RTZR4308/PrintModels/Other/Tube_fixator.stl

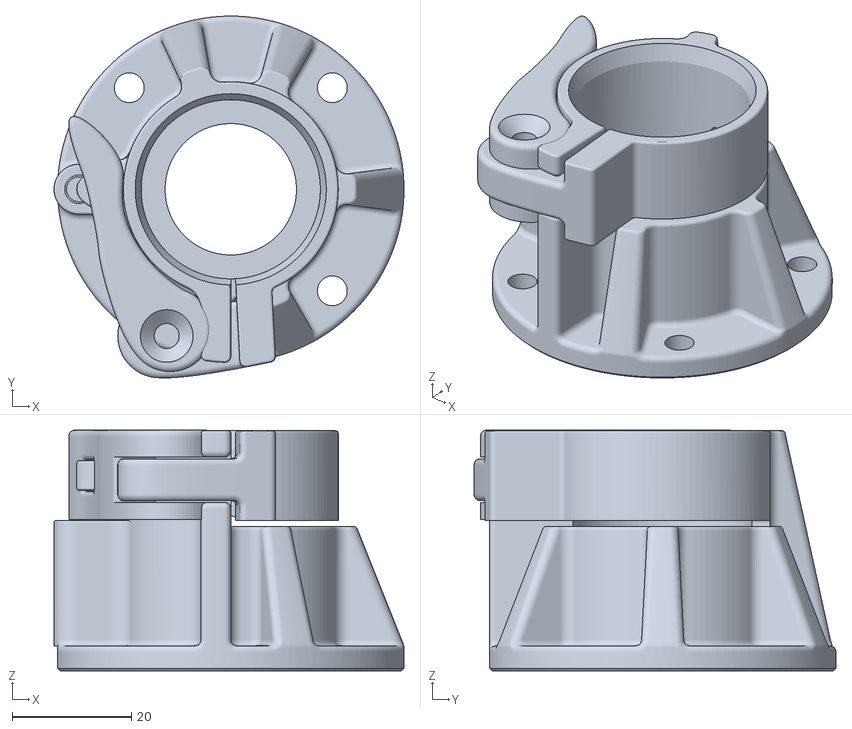
[picture p15: CAD file, 2025-07-25]
Other/Tube_fixator.stl
58.6 x 60.6 x 40.3
