RTZR4308/PrintModels/Starlink/Reductor Starlink.step

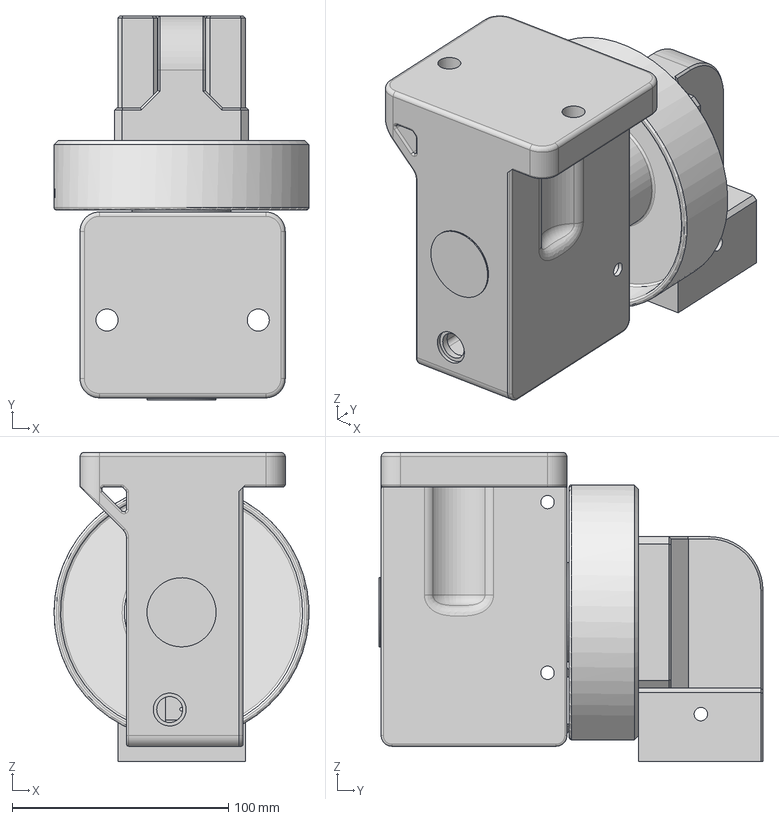
[picture p16: CAD file, 2025-03-28]
Starlink/Reductor Starlink.step
117.9 x 177.7 x 143.1 mm
OutputFile
BS 4320 - M6 G Steel 100 HV Plain
DIN 933 - M6 x 80 Steel 4.6 Plain x 2
DIN 912 - M5 x 0.8 x 20 Steel 4.6 Plain x 4
