RTZR4308/PrintModels/Autel/autel_4tmax_leg_rf.stl

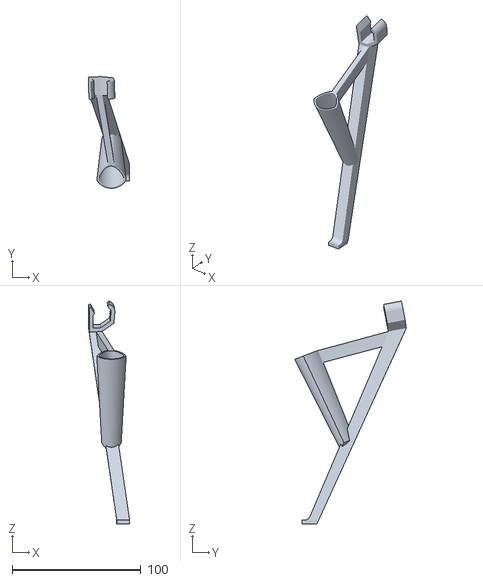
[picture p17: CAD file, 2024-12-12]
Autel/autel_4tmax_leg_rf.stl
32.1 x 86.9 x 173.5
