RTZR4308/PrintModels/Autel/Dual Bat/autel_top_holder_front_V2.STL

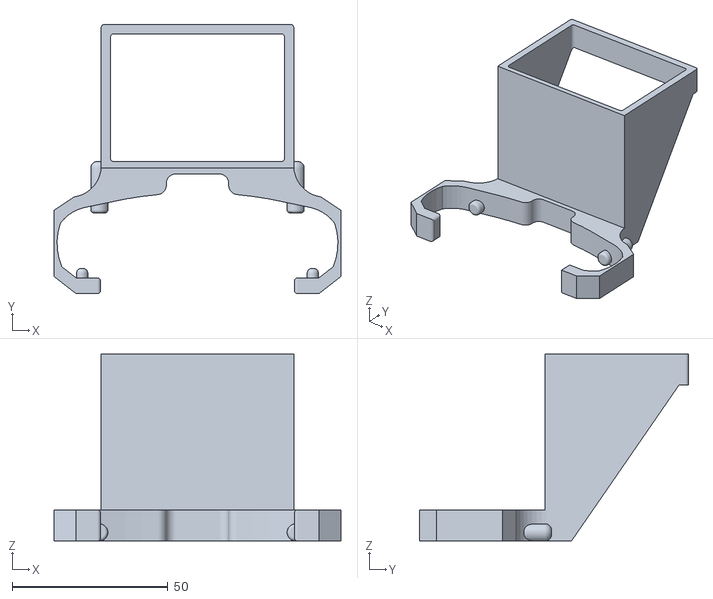
[picture p18: CAD file, 2025-02-19]
Autel/Dual Bat/autel_top_holder_front_V2.STL
92.1 x 86.4 x 60.0
