RTZR4308/PrintModels/Controllers/rm510_4Ntype_Mount_air.STL

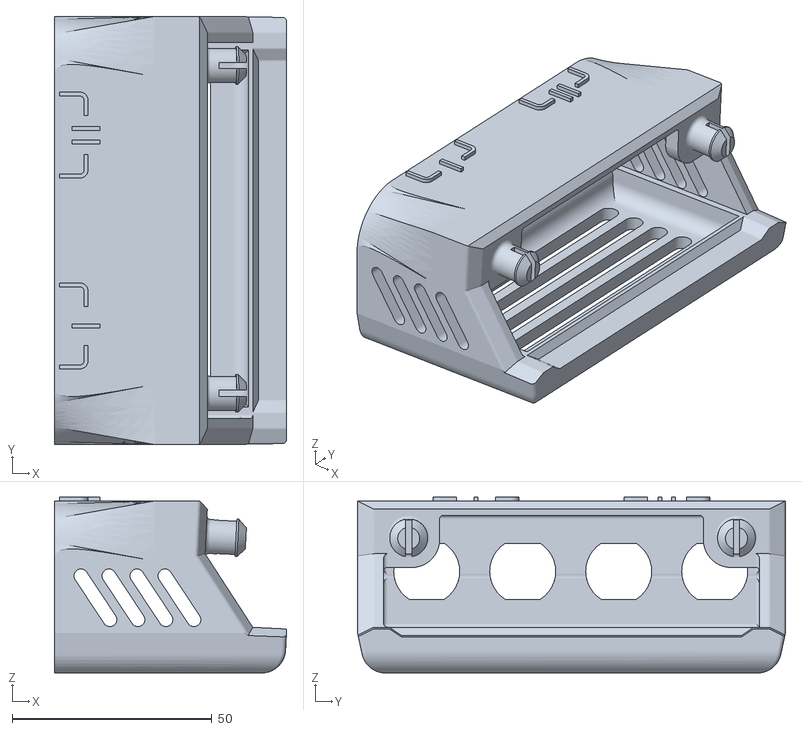
[picture p19: CAD file, 2024-12-12]
Controllers/rm510_4Ntype_Mount_air.STL
58.1 x 107.0 x 44.0
