RTZR4308/PrintModels/DJI/M3/Dual Bat/dji_m3_dual_bat_fpv_99scale_8parts_x1c.3mf

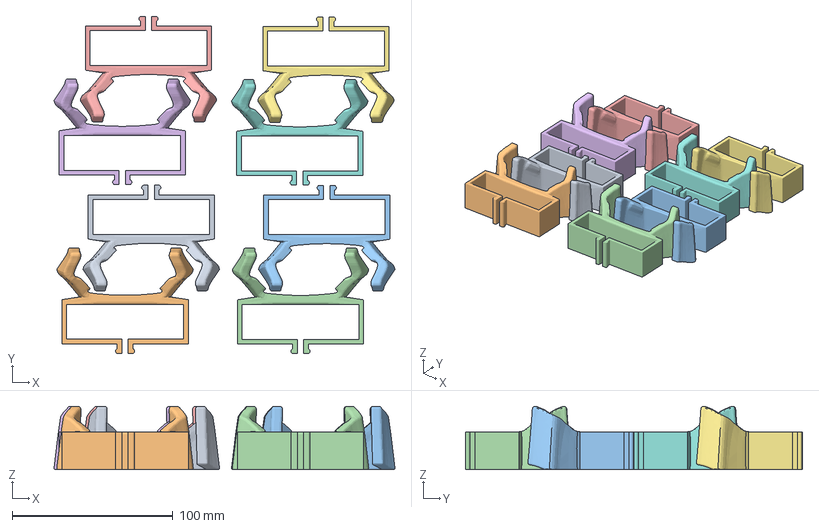
[picture p20: CAD file, 2025-01-25]
DJI/M3/Dual Bat/dji_m3_dual_bat_fpv_99scale_8parts_x1c.3mf
212.1 x 209.9 x 39.4 mm
dji_m3_dual_bat_fpv.stl x 8
