RTZR4308/PrintModels/DJI/M3/Legs/dji_m3_leg_bl.stl

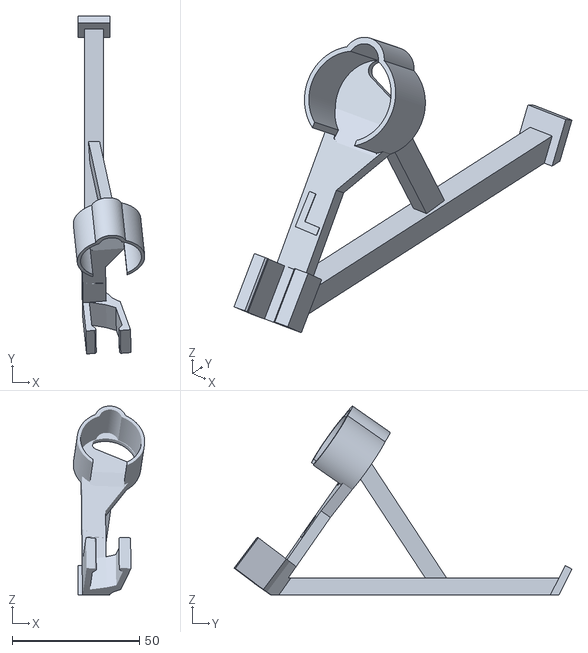
[picture p21: CAD file, 2024-12-12]
DJI/M3/Legs/dji_m3_leg_bl.stl
28.0 x 132.6 x 74.1
