RTZR4308/PrintModels/DJI/M4/dji_m4_double_bat.step

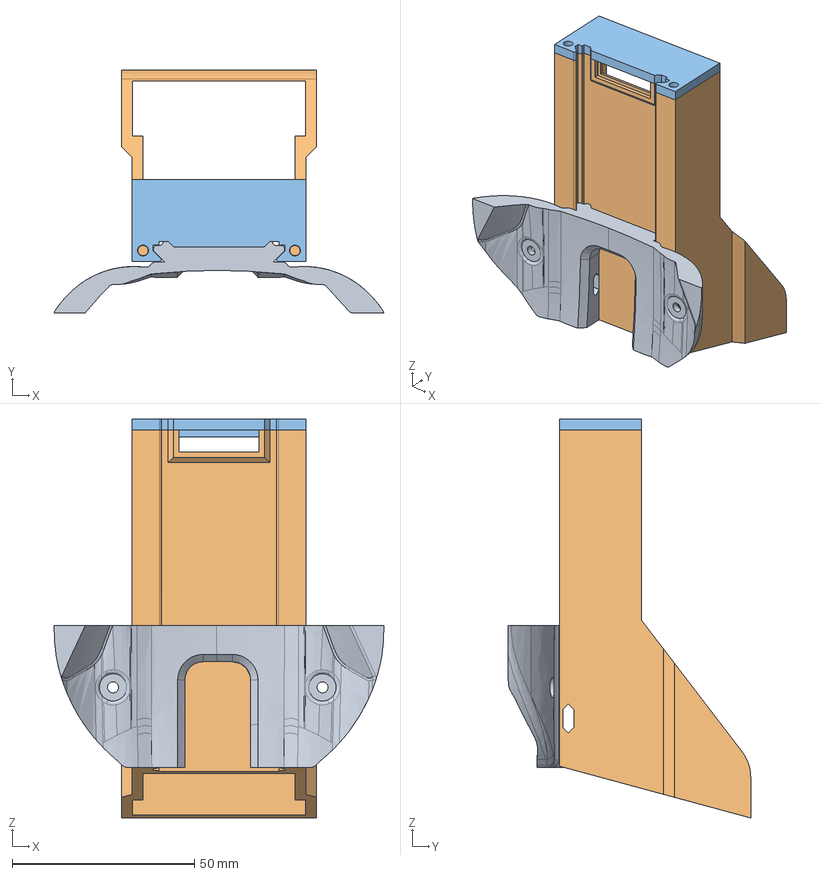
[picture p22: CAD file, 2025-07-25]
DJI/M4/dji_m4_double_bat.step
90.5 x 66.6 x 109.5 mm
KR.M4T.001
KR.M4T.002
KR.M4T.005
