RTZR4308/PrintModels/DJI/Mini Yoyo/dji_m3_pro_mini_yoyo_mount.stl

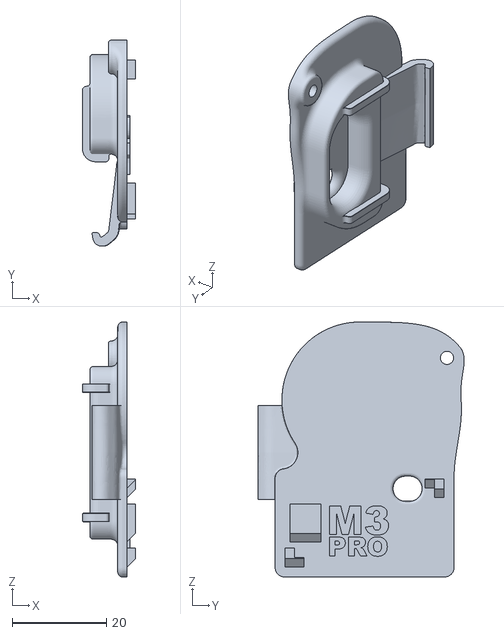
[picture p23: CAD file, 2025-07-26]
DJI/Mini Yoyo/dji_m3_pro_mini_yoyo_mount.stl
11.3 x 43.7 x 54.0
