RTZR4308/PrintModels/DJI/RM510B/Ntype/dji_rm510b_4Ntype_mount_hdmi.STL

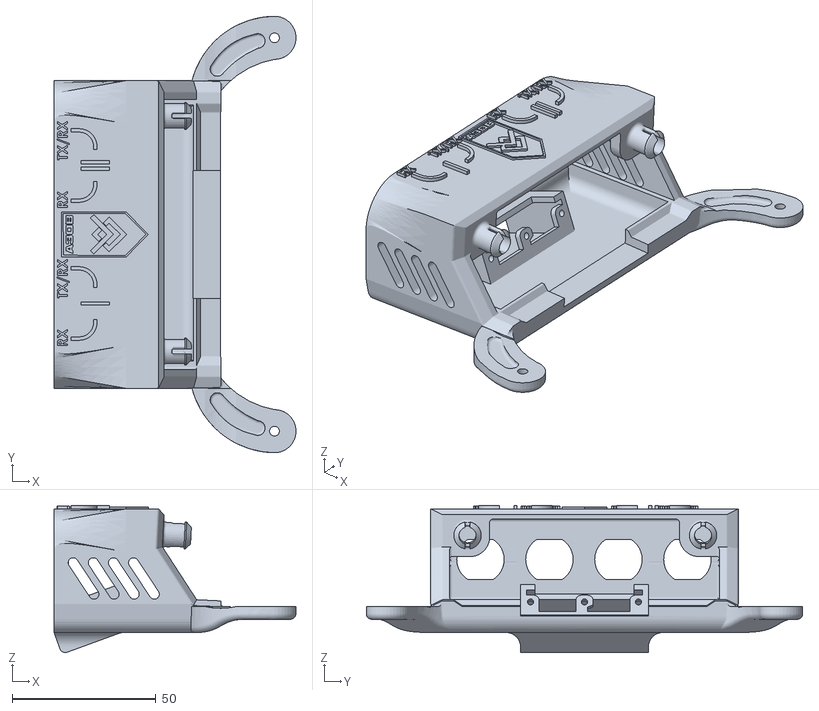
[picture p24: CAD file, 2025-05-24]
DJI/RM510B/Ntype/dji_rm510b_4Ntype_mount_hdmi.STL
84.2 x 151.8 x 51.2
