RTZR4308/PrintModels/DJI/RM700B/dji_rm700b_N_type_holder.3mf

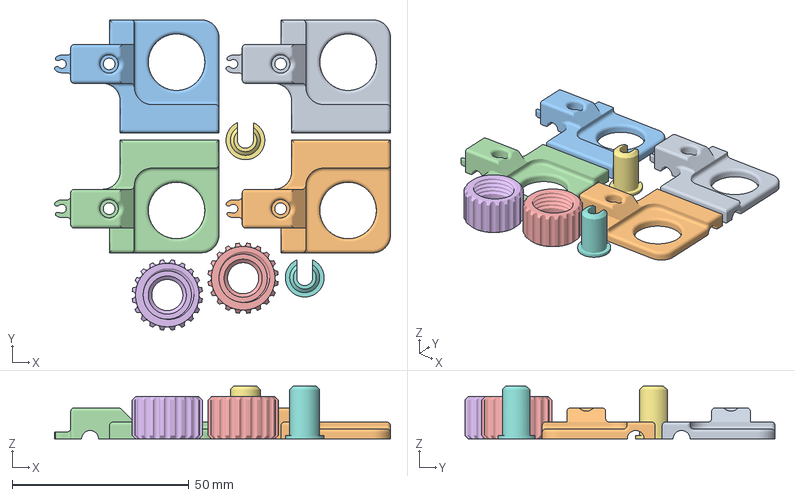
[picture p25: CAD file, 2025-03-28]
DJI/RM700B/dji_rm700b_N_type_holder.3mf
95.2 x 87.9 x 15.0 mm
dji_rm700b_N_type_holder.STL
dji_rm700b_N_type_holder_mirror.STL
dji_rm700b_n_type_holder_r02.STL
dji_rm700b_N_type_holder_mirror_r02.STL
dji_rm700b_Nut_v04.STL x 2
dji_rm700b_spacer_v05.STL x 2
