RTZR4308/PrintModels/Other/Tube_holder.stl

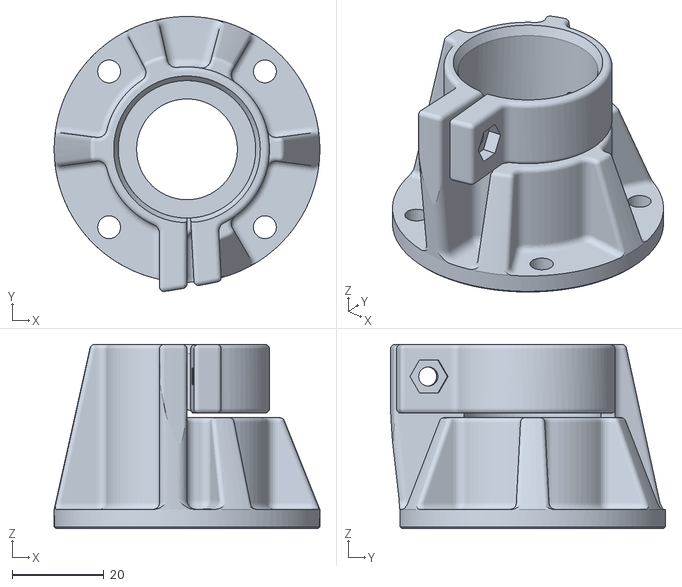
[picture p26: CAD file, 2025-07-25]
Other/Tube_holder.stl
58.0 x 60.0 x 40.2
