RTZR4308/PrintModels/Starlink/starlink_leg_cap_azov_101scale.3mf

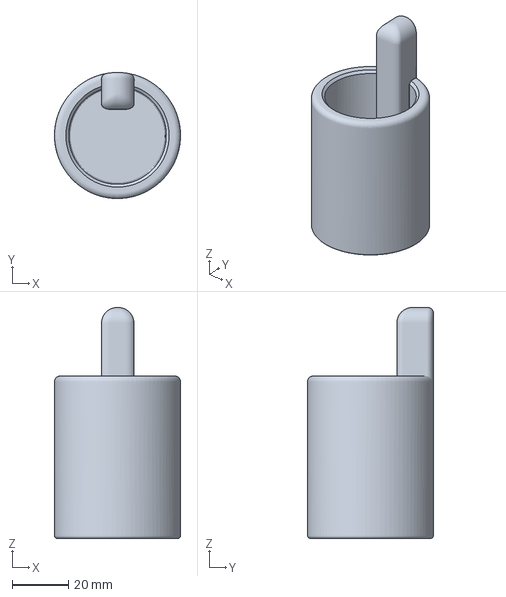
[picture p27: CAD file, 2025-01-25]
Starlink/starlink_leg_cap_azov_101scale.3mf
44.6 x 44.6 x 81.8 mm
