RTZR4308/PrintModels/DJI/M3/Dual Bat/dji_m3_dual_bat_99scale_8parts_x1c.3mf

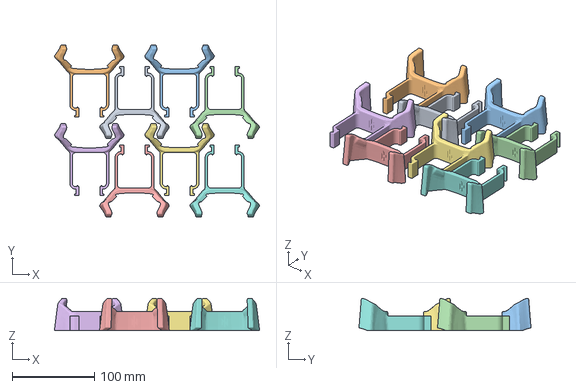
[picture p28: CAD file, 2024-12-28]
DJI/M3/Dual Bat/dji_m3_dual_bat_99scale_8parts_x1c.3mf
249.9 x 209.8 x 39.4 mm
dji_m3_dual_bat.stl x 8
