RTZR4308/PrintModels/DJI/M3/Legs/dji_m3_leg_fl.stl

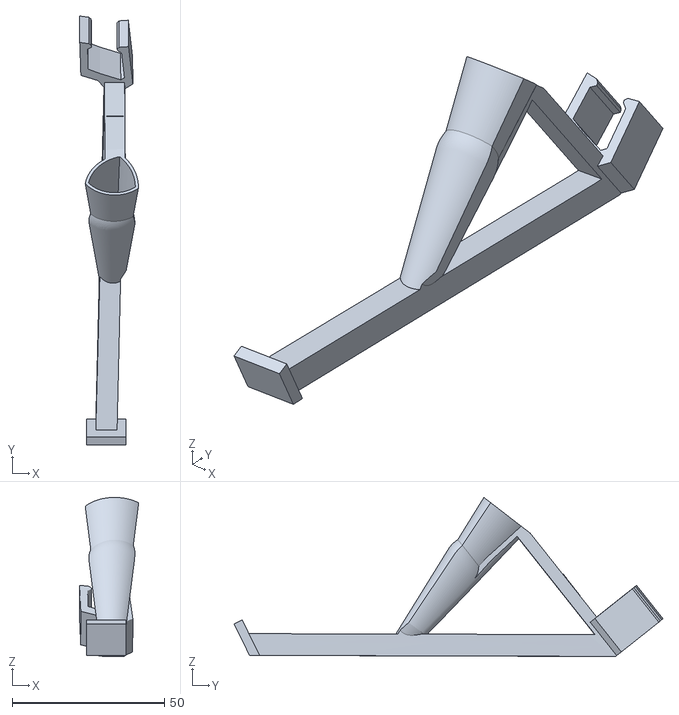
[picture p29: CAD file, 2024-12-12]
DJI/M3/Legs/dji_m3_leg_fl.stl
19.4 x 141.0 x 52.3
