RTZR4308/PrintModels/DJI/M4/dji_m4_arm_bracket.stl

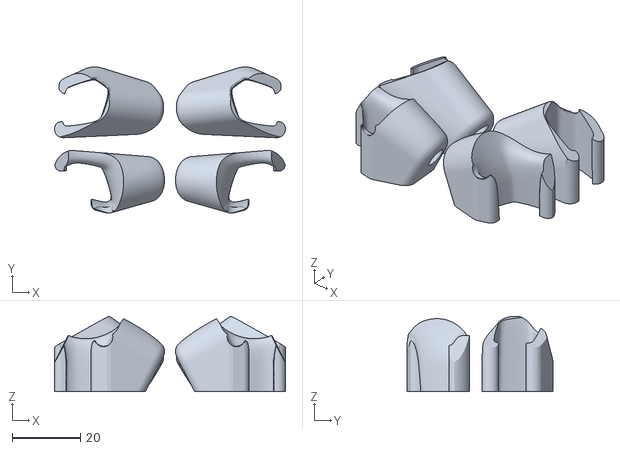
[picture p30: CAD file, 2025-05-24]
DJI/M4/dji_m4_arm_bracket.stl
67.6 x 42.8 x 22.1
