RTZR4308/PrintModels/DJI/Mini Yoyo/dji_m3_mini_yoyo_mount.stl

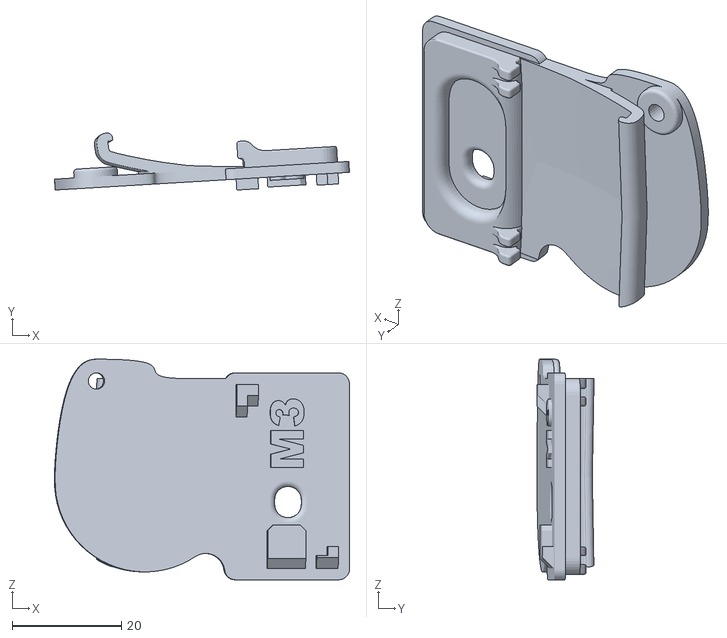
[picture p31: CAD file, 2025-07-25]
DJI/Mini Yoyo/dji_m3_mini_yoyo_mount.stl
54.0 x 10.5 x 40.4
