RTZR4308/PrintModels/DJI/RM700B/dji_rm700b_N_type_holder_mirror.STL

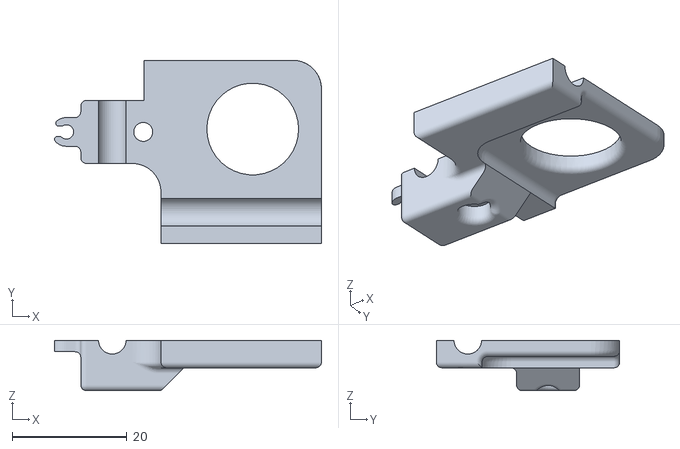
[picture p32: CAD file, 2025-02-19]
DJI/RM700B/dji_rm700b_N_type_holder_mirror.STL
46.6 x 32.0 x 8.80
