RTZR4308/PrintModels/Other/Bumblbee_arm.STL

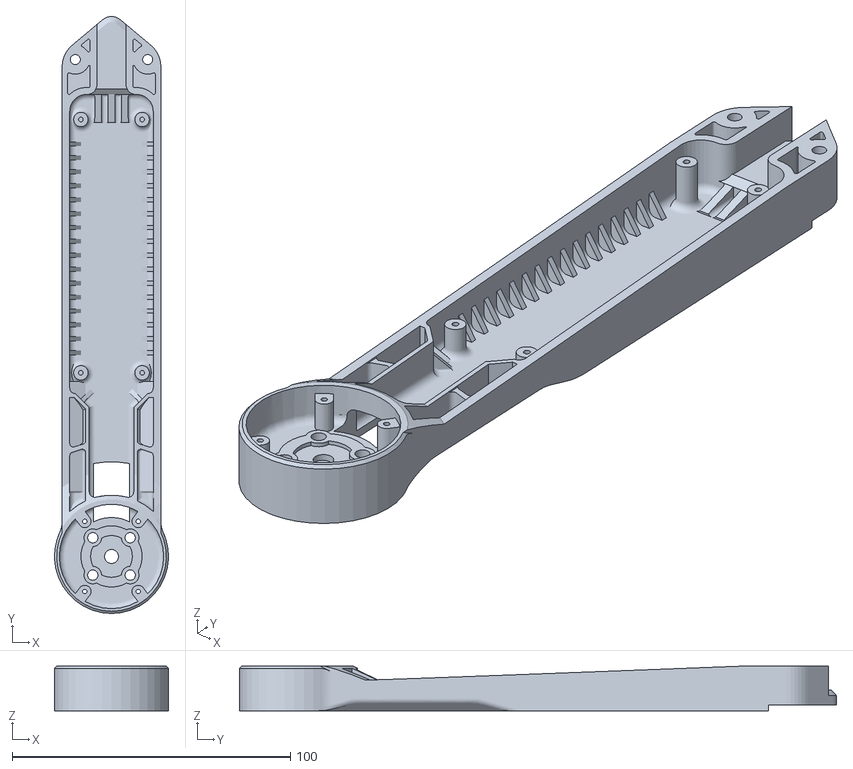
[picture p33: CAD file, 2025-07-04]
Other/Bumblbee_arm.STL
41.0 x 214.5 x 16.0
