RTZR4308/PrintModels/Starlink/starlink_leg_cap_azov.stl

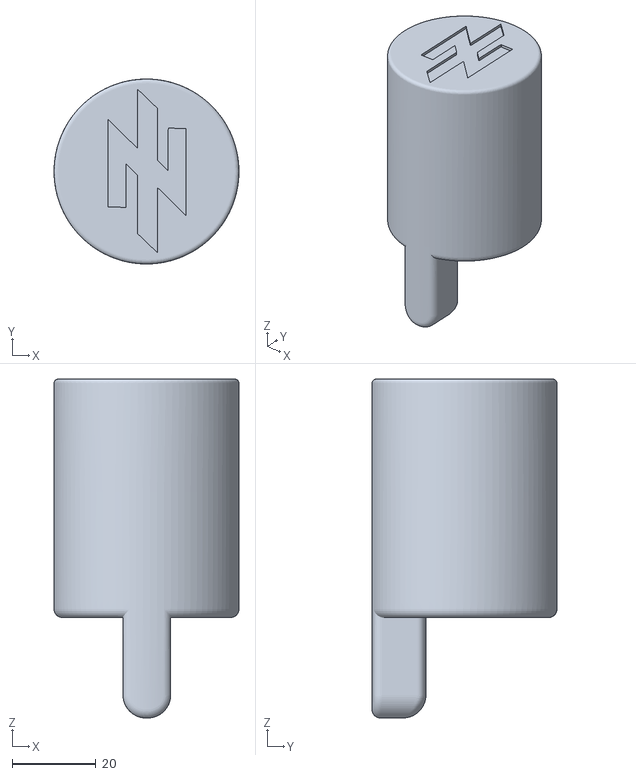
[picture p34: CAD file, 2025-01-25]
Starlink/starlink_leg_cap_azov.stl
44.2 x 44.2 x 81.0
