RTZR4308/PrintModels/Controllers/2Ntype_Mount_air_wings.STL

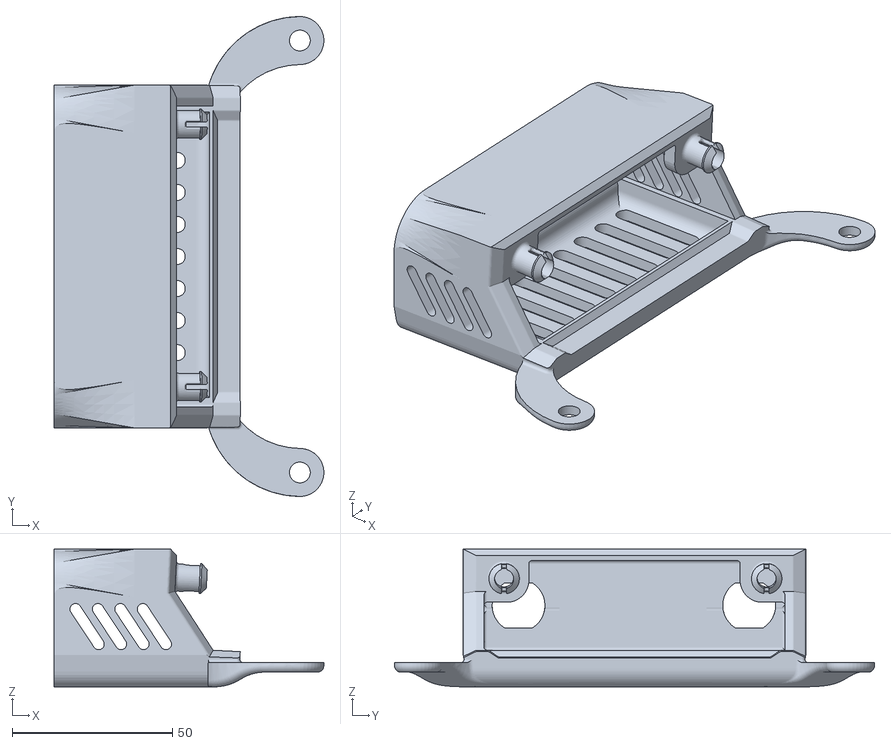
[picture p35: CAD file, 2024-12-12]
Controllers/2Ntype_Mount_air_wings.STL
84.2 x 149.8 x 43.0
