RTZR4308/PrintModels/DJI/M3/Dual Bat/dji_m3_dual_bat.stl

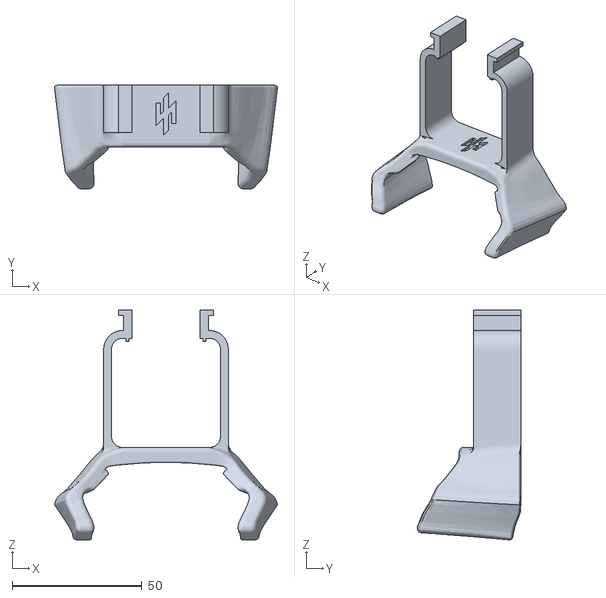
[picture p36: CAD file, 2024-12-12]
DJI/M3/Dual Bat/dji_m3_dual_bat.stl
85.8 x 39.8 x 88.4
