RTZR4308/PrintModels/DJI/Mini Yoyo/dji_m4t_mini_yoyo_mount.stl

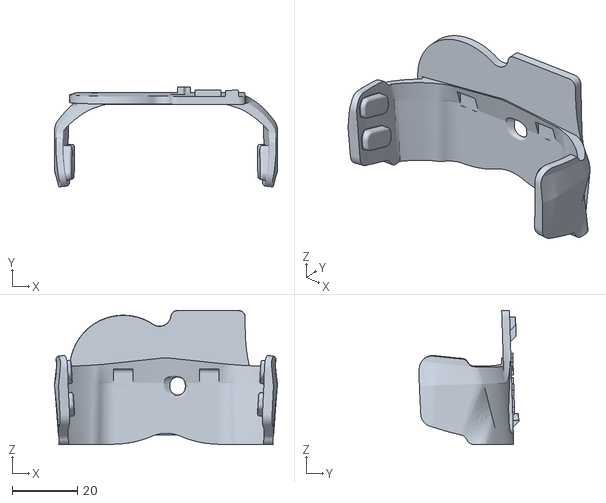
[picture p37: CAD file, 2025-07-25]
DJI/Mini Yoyo/dji_m4t_mini_yoyo_mount.stl
68.6 x 30.7 x 41.3
