RTZR4308/PrintModels/DJI/RM510B/Ntype/dji_rm510b_4Ntype_RTZR_mount_hdmi_kit_ x1.3mf

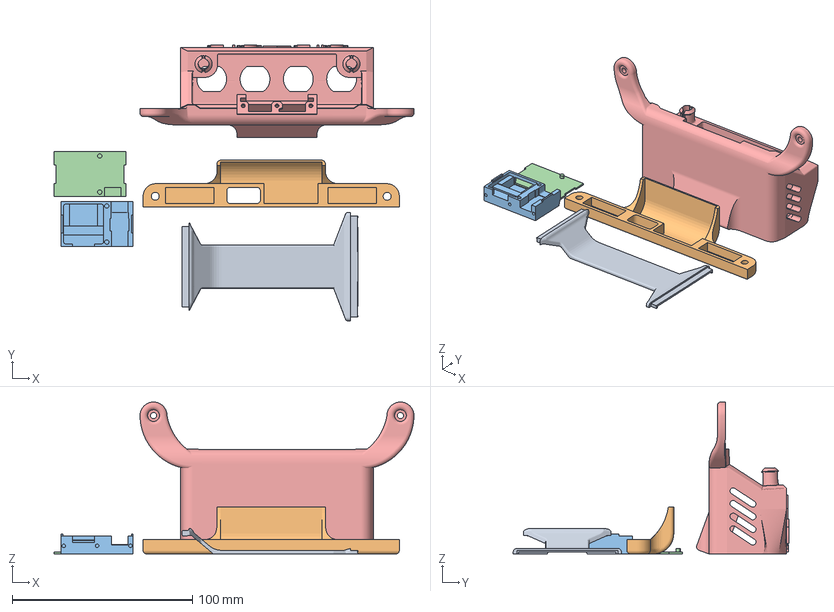
[picture p38: CAD file, 2025-05-24]
DJI/RM510B/Ntype/dji_rm510b_4Ntype_RTZR_mount_hdmi_kit_ x1.3mf
199.5 x 152.7 x 84.2 mm
cable_tunnel.STL
bottom_holder.STL
hdmi_holder.STL
hdmi_holder_cover.STL
dji_rm510b_4Ntype_mount_hdmi_RTZR.step
