RTZR4308/PrintModels/Other/Reductor ST-box v17.3mf

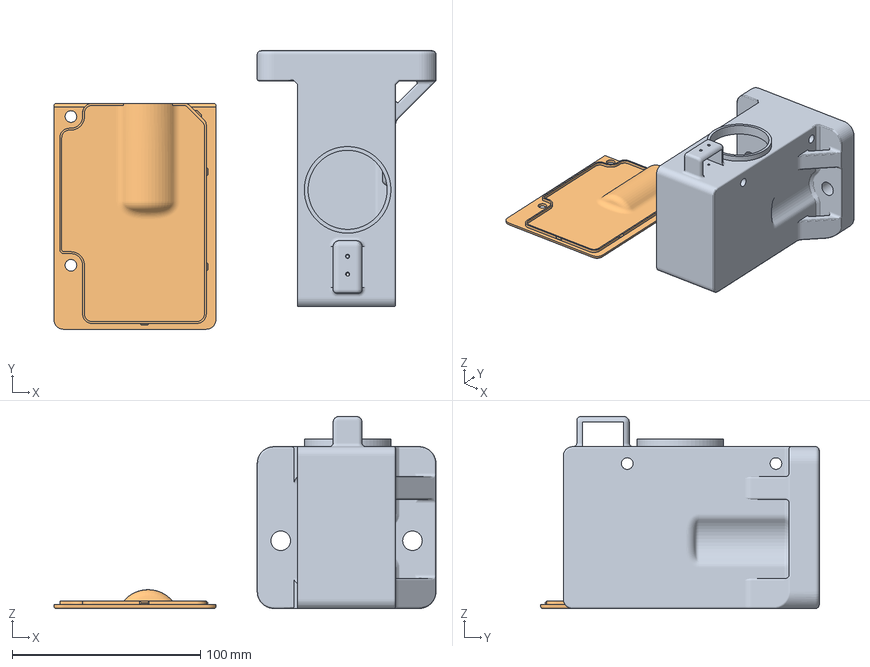
[picture p39: CAD file, 2025-05-24]
Other/Reductor ST-box v17.3mf
202.9 x 148.0 x 102.0 mm
Reductor ST-box v19.stl_1
Reductor ST-box v19.stl_2
