RTZR4308/PrintModels/DJI/Mini Yoyo/mini_yoyo.stl

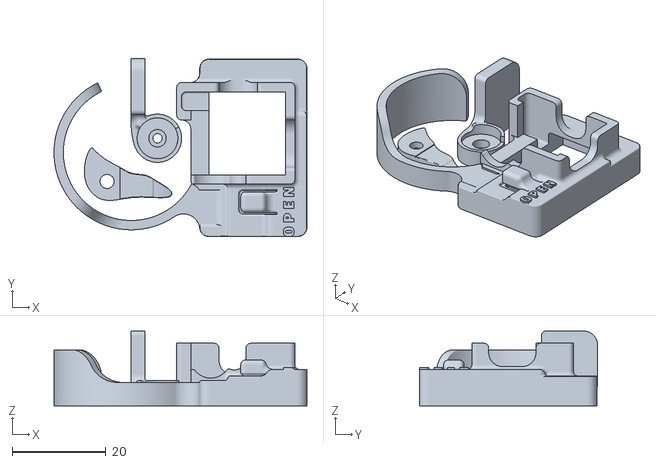
[picture p40: CAD file, 2025-07-05]
DJI/Mini Yoyo/mini_yoyo.stl
54.0 x 38.0 x 16.0
