RTZR4308/PrintModels/DJI/RM510B/Ntype/dji_rm510b_4Ntype_IN_mount_hdmi_kit_ x1.3mf

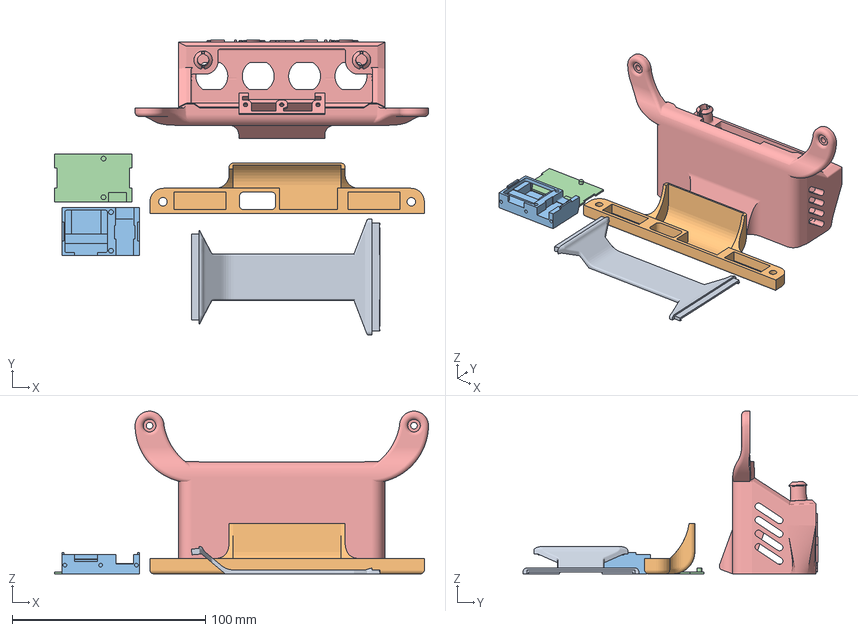
[picture p41: CAD file, 2025-05-24]
DJI/RM510B/Ntype/dji_rm510b_4Ntype_IN_mount_hdmi_kit_ x1.3mf
193.5 x 152.8 x 84.2 mm
cable_tunnel.STL
bottom_holder.STL
hdmi_holder.STL
hdmi_holder_cover.STL
dji_rm510b_4Ntype_mount_hdmi_IN.step
