RTZR4308/PrintModels/Other/Dzyga.step

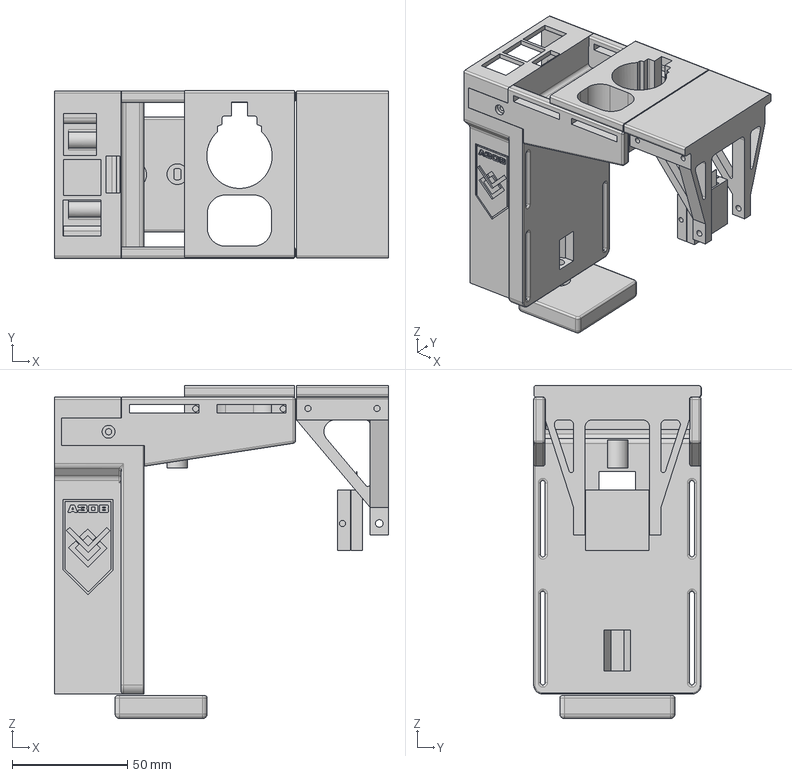
[picture p42: CAD file, 2025-03-28]
Other/Dzyga.step
145.1 x 72.9 x 144.8 mm
Case
RPi cam Rev 1.3
Motor case
Camera holder
Adapter
