RTZR4308/PrintModels/DJI/Mini Yoyo/yoyo_cartridge_24_set.3mf

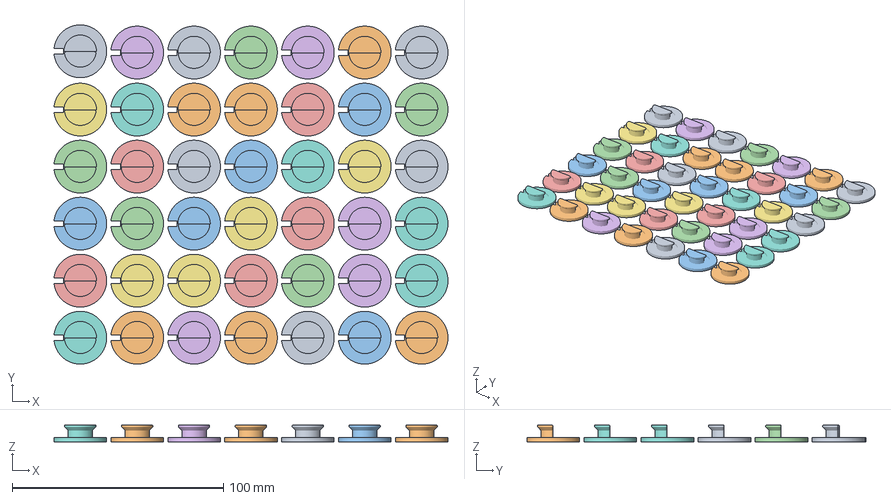
[picture p43: CAD file, 2025-07-05]
DJI/Mini Yoyo/yoyo_cartridge_24_set.3mf
186.5 x 160.6 x 8.00 mm
yoyo_cartrige.stl 33 x 42
