RTZR4308/PrintModels/DJI/RM510B/Ntype/dji_rm510b_Ntype_plug.step

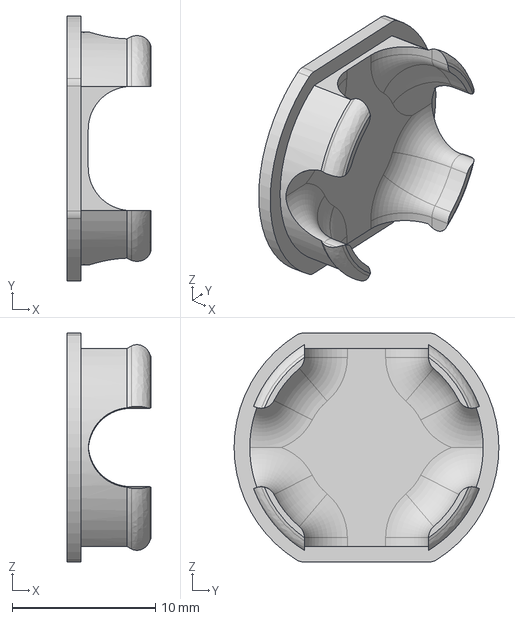
[picture p44: CAD file, 2025-03-28]
DJI/RM510B/Ntype/dji_rm510b_Ntype_plug.step
5.90 x 18.5 x 16.0 mm
