RTZR4308/PrintModels/Other/Lira Type-C.step

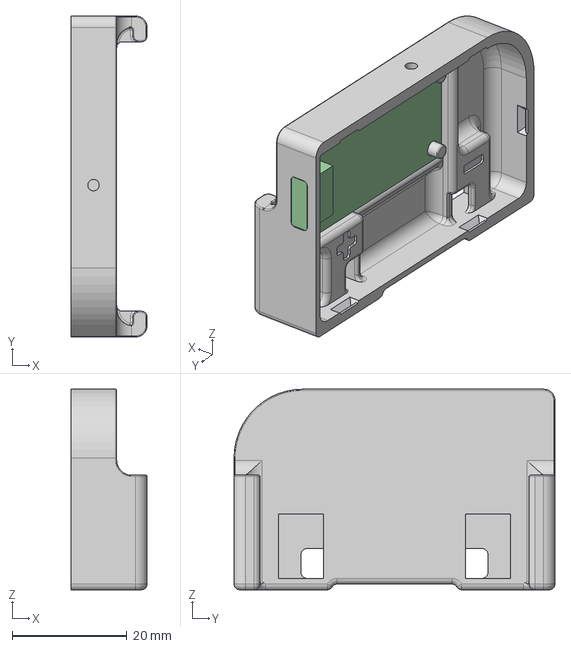
[picture p45: CAD file, 2025-02-19]
Other/Lira Type-C.step
13.3 x 56.0 x 35.0 mm
