RTZR4308/PrintModels/DJI/Mini Yoyo/yoyo_cartridge.stl

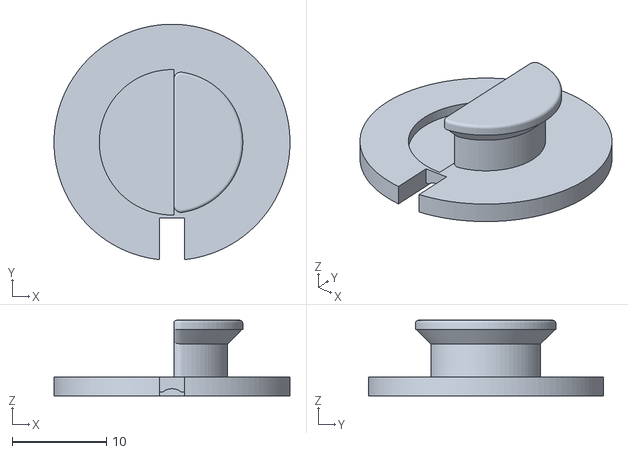
[picture p46: CAD file, 2025-07-05]
DJI/Mini Yoyo/yoyo_cartridge.stl
25.0 x 24.9 x 8.00
