RTZR4308/PrintModels/DJI/RM510B/Ntype/dji_rm510b_4Ntype_mount_hdmi_IN.step

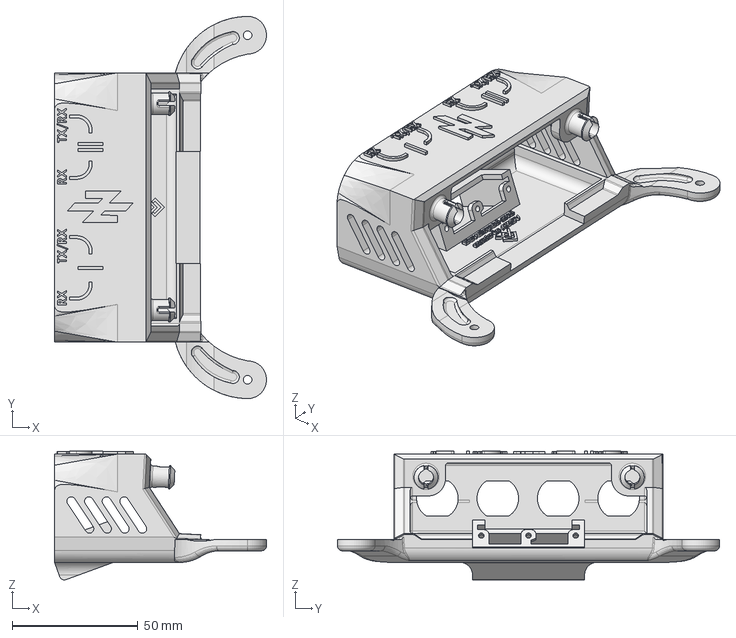
[picture p47: CAD file, 2025-03-28]
DJI/RM510B/Ntype/dji_rm510b_4Ntype_mount_hdmi_IN.step
84.2 x 151.8 x 51.2 mm
