RTZR4308/PrintModels/DJI/RM700B/dji_rm700b_spacer_v05.STL

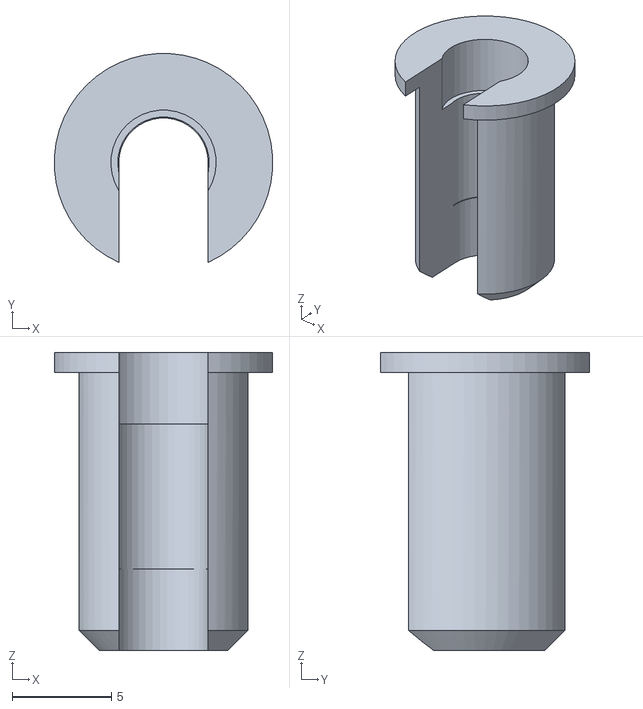
[picture p48: CAD file, 2025-02-19]
DJI/RM700B/dji_rm700b_spacer_v05.STL
11.0 x 10.5 x 15.0
