RTZR4308/PrintModels/Other/Generator switch handle.stl

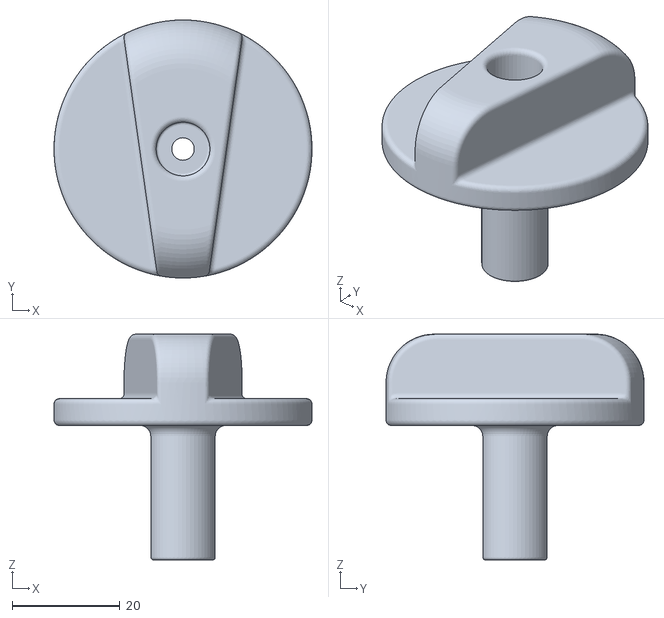
[picture p49: CAD file, 2025-02-19]
Other/Generator switch handle.stl
48.0 x 48.0 x 42.0
