RTZR4308/PrintModels/Other/Alientech_double_mount.STL

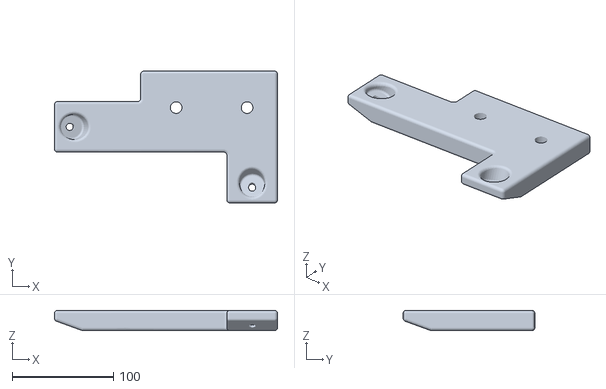
[picture p50: CAD file, 2025-02-19]
Other/Alientech_double_mount.STL
220.0 x 130.0 x 20.0
