RTZR4308/PrintModels/DJI/RM510B/Ntype/dji_rm510b_4Ntype_mount.STL

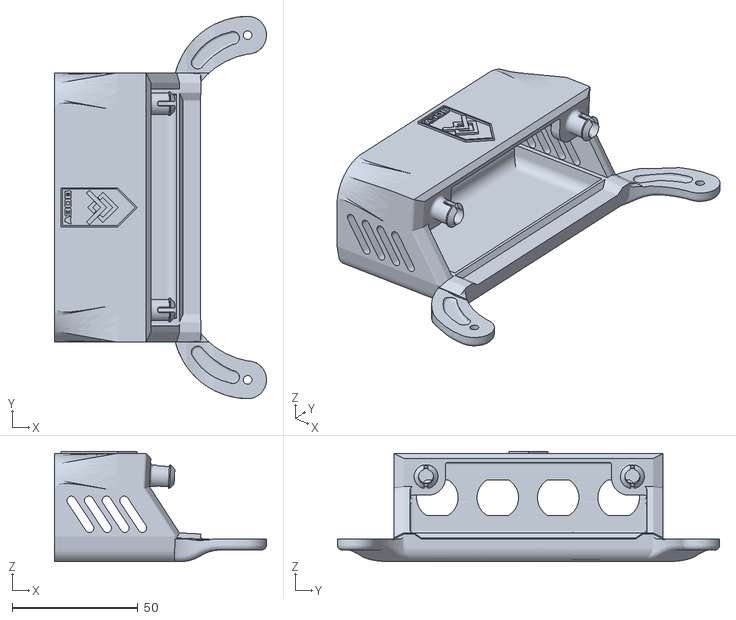
[picture p52: CAD file, 2024-12-17]
DJI/RM510B/Ntype/dji_rm510b_4Ntype_mount.STL
84.2 x 151.8 x 43.8
