RTZR4308/PrintModels/DJI/RM510B/Ntype/dji_rm510b_bottom_holder.STL

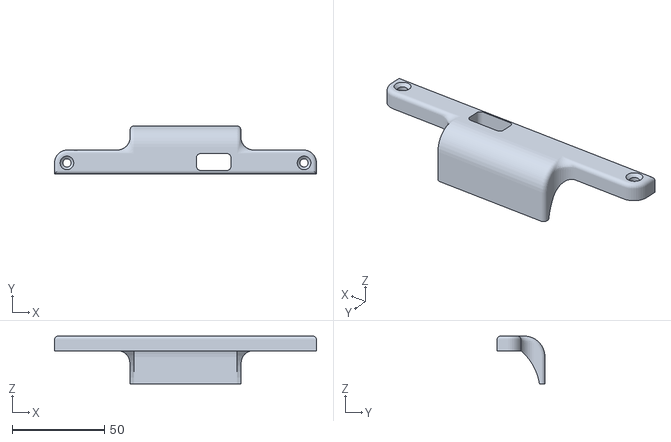
[picture p53: CAD file, 2024-12-17]
DJI/RM510B/Ntype/dji_rm510b_bottom_holder.STL
142.0 x 26.0 x 26.0
