RTZR4308/PrintModels/DJI/RM510B/Ntype/dji_rm510b_cable_tunnel.STL

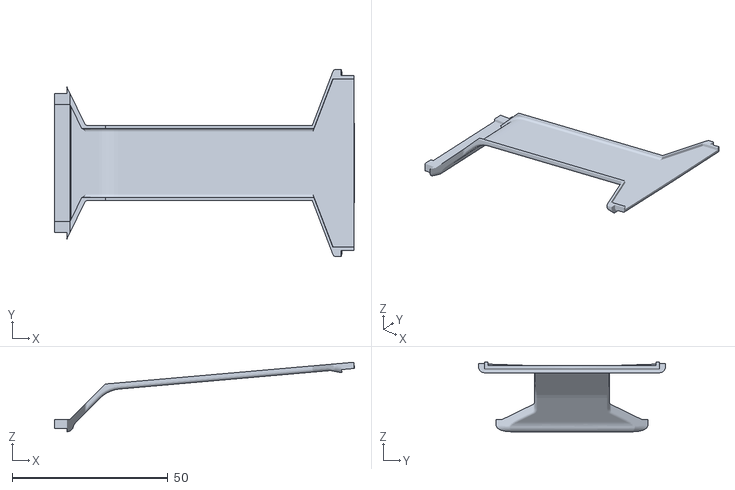
[picture p55: CAD file, 2024-12-17]
DJI/RM510B/Ntype/dji_rm510b_cable_tunnel.STL
96.2 x 60.0 x 22.3
