RTZR4308/PrintModels/DJI/RM510B/Ntype/dji_rm510b_hdmi_holder.STL

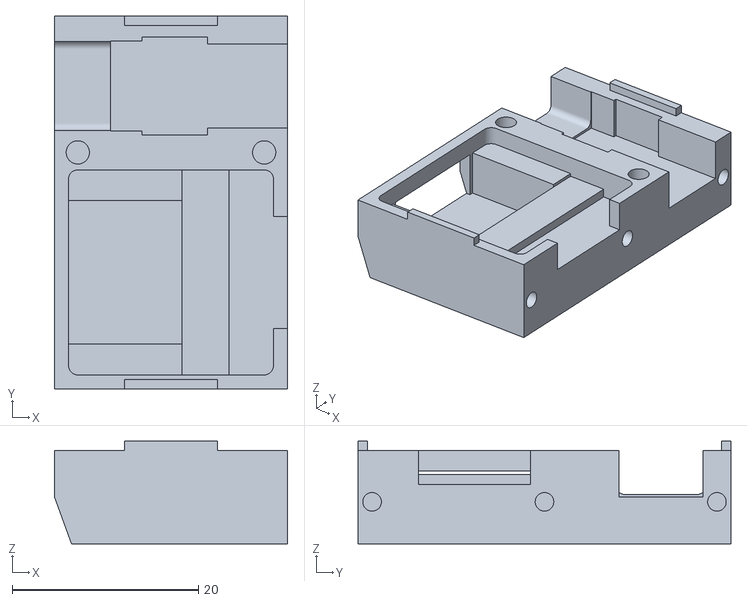
[picture p56: CAD file, 2024-12-17]
DJI/RM510B/Ntype/dji_rm510b_hdmi_holder.STL
25.0 x 40.0 x 11.0
